acowls/MeterClock/as-built/enclosure-side+front.jpeg

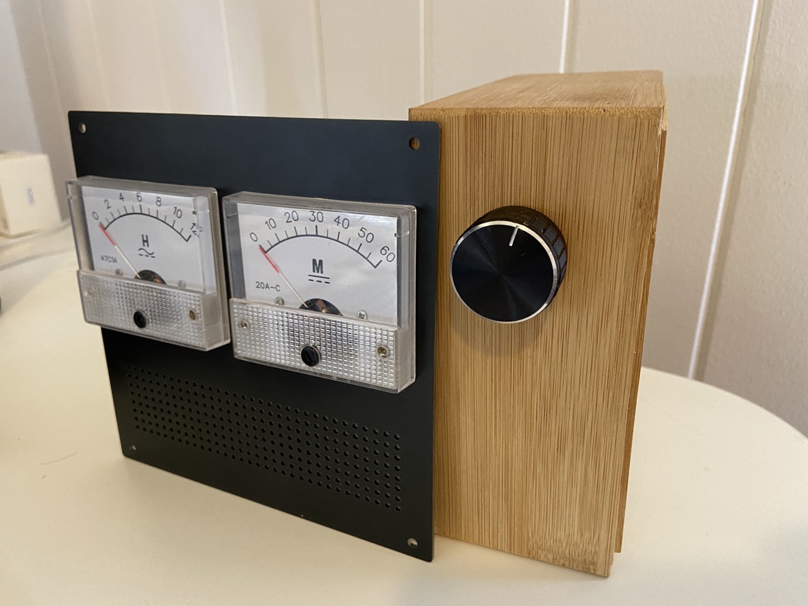
as-built/enclosure-side+front.jpeg
