acowls/MeterClock/as-built/fritzing-layout.png

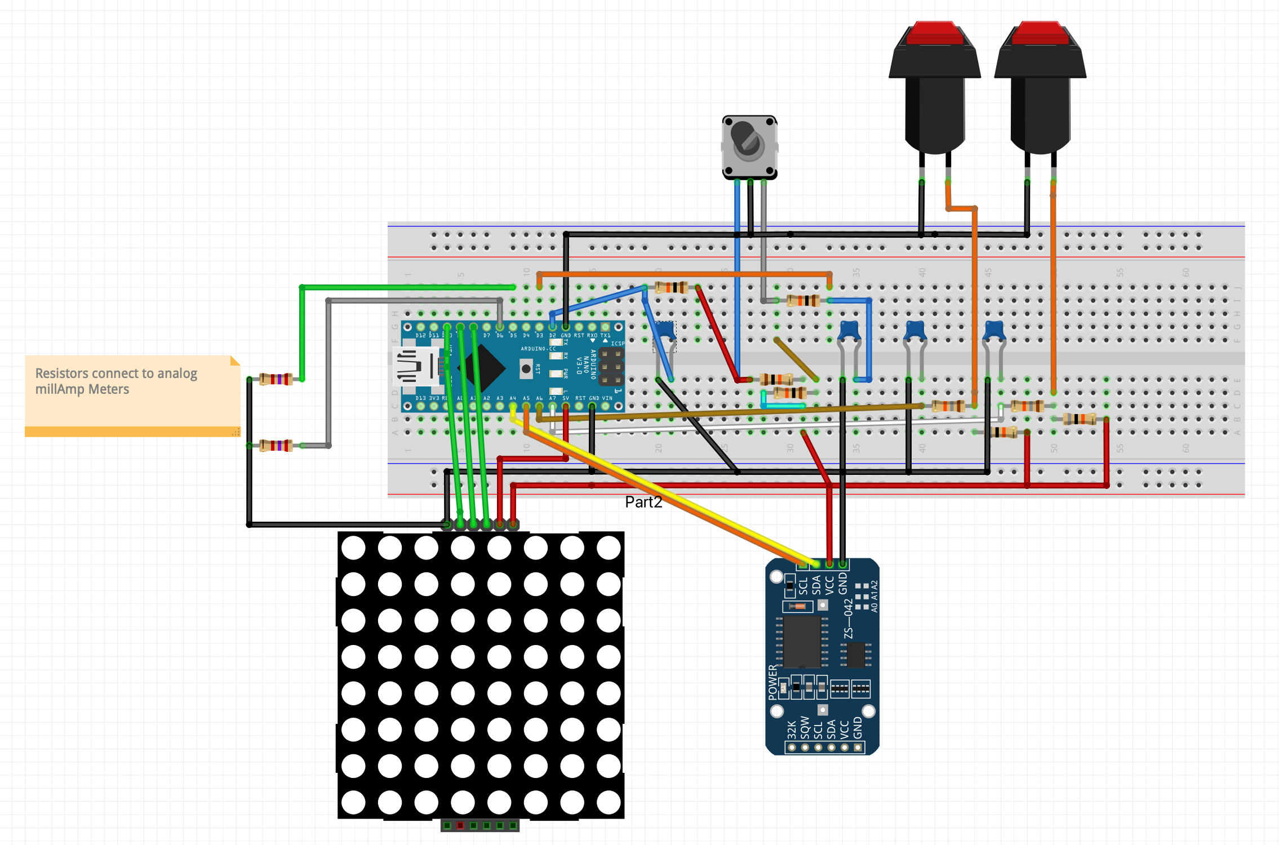
as-built/fritzing-layout.png
