acowls/MeterClock/as-built/mainboard-layout.png

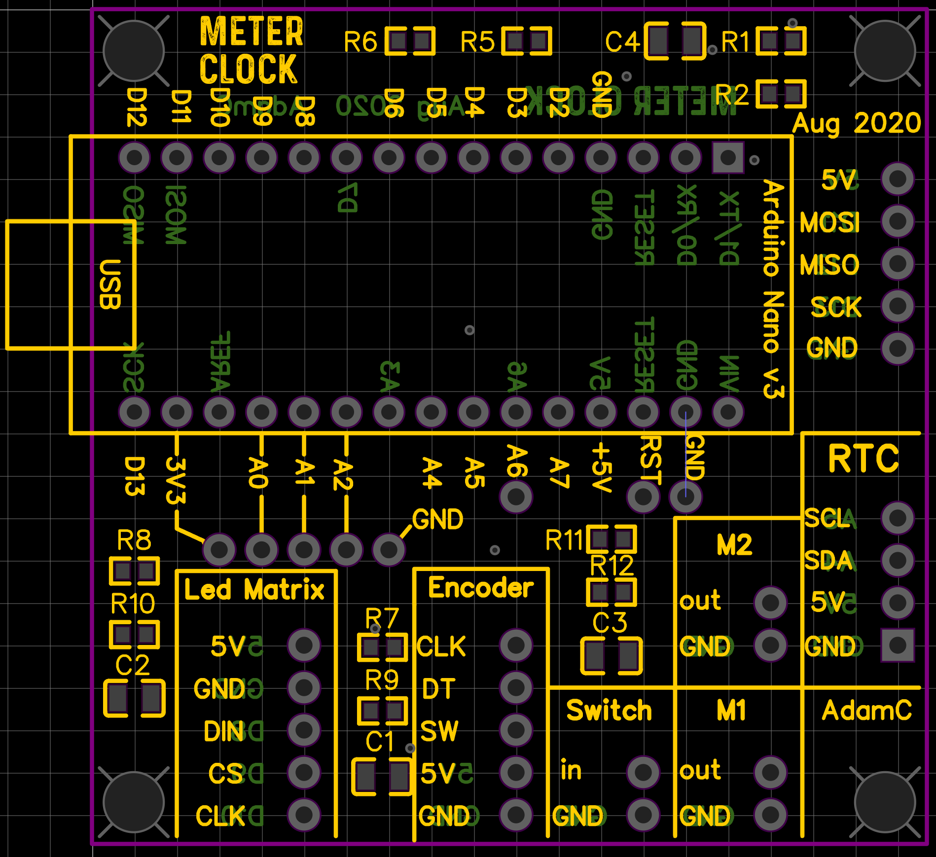
as-built/mainboard-layout.png
