acowls/MeterClock/as-built/meter-panels.jpeg

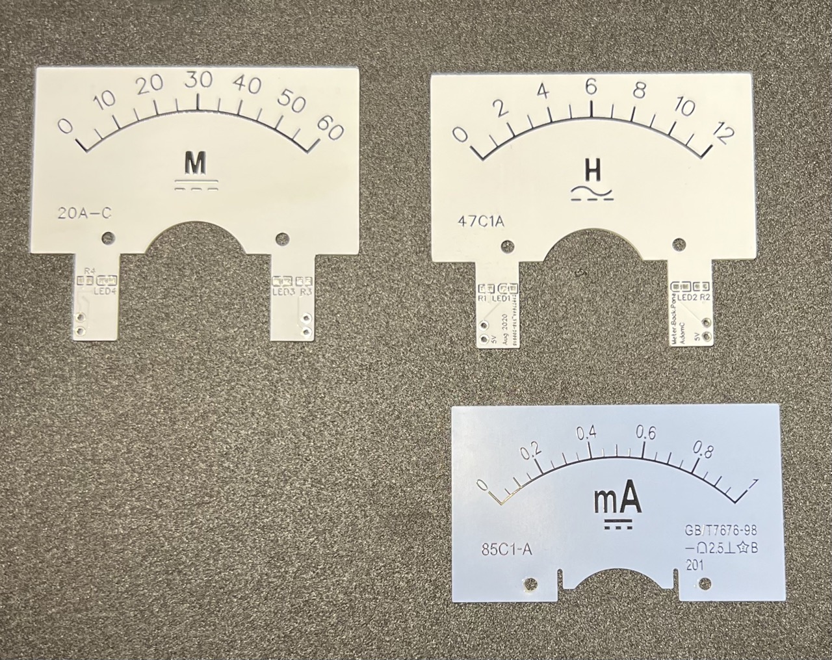
as-built/meter-panels.jpeg
