acowls/MeterClock/as-built/meter-side2-render.png

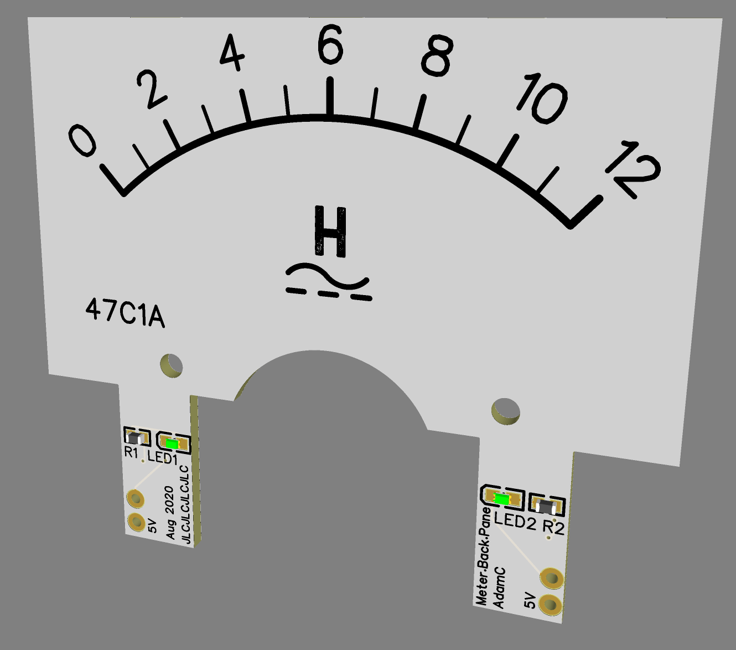
as-built/meter-side2-render.png
