acowls/MeterClock/parts/kmart-bamboo-drawer-tidy.png

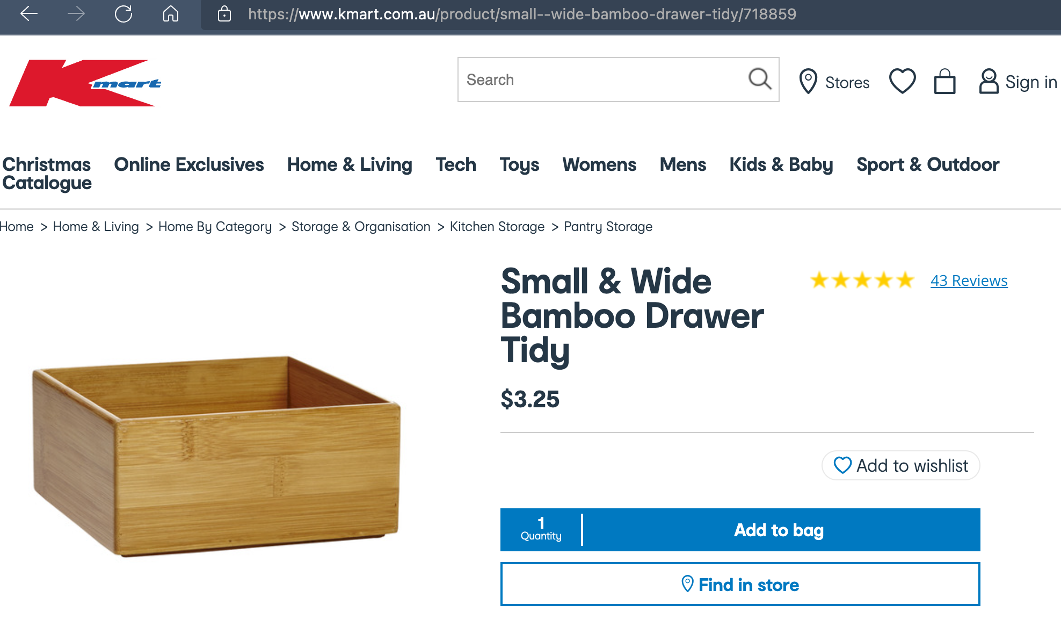
parts/kmart-bamboo-drawer-tidy.png
